KavinV125/Water_-Quality_mointer/PCB Module/layout.png

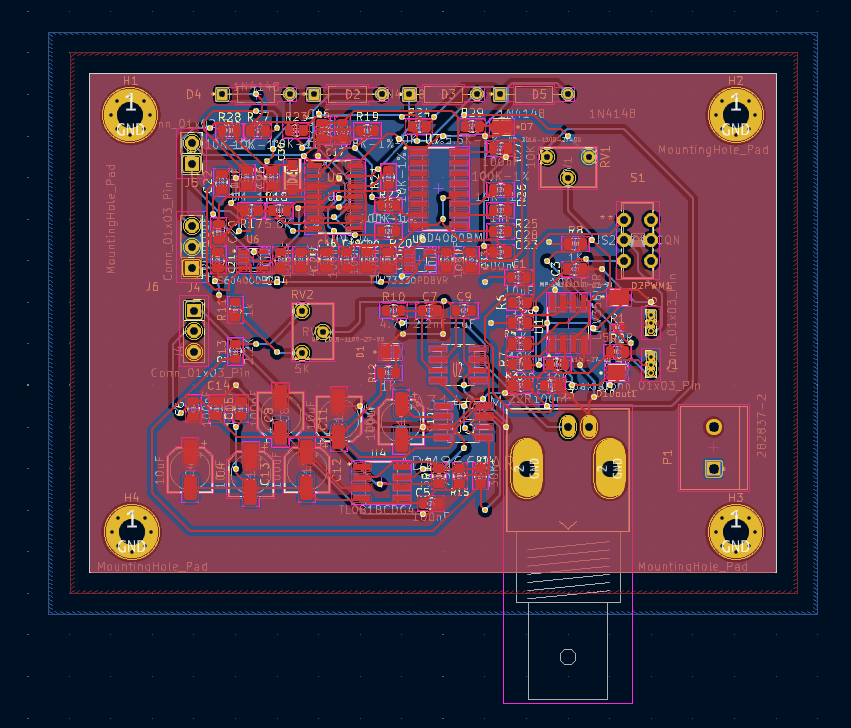
PCB Module/layout.png
